hubjab21/high-speed-analog-front-end-pcb/LTspice/lmh5401_test.asc

C1: cap; 5p
C2: cap; 2.2n
C3: cap; 2.2n
C4: cap; 2.2n
R8: res; 50
R9: res; 50
R10: res; 210
R11: res; 210
RF+: res; 100k
RF-: res; 100k
RG+: res; 470
RG-: res; 470
Rin: res; 50
RM: res; 0
RT: res; 100k
U1: LMH5401
V1: voltage; -2.5
V2: voltage; 2.5
Vin: voltage; ""; AC 10m
Named nets: 0, OUT+, OUT-
.include LMH5401.lib
.ac dec 1000 100 1G
.tran 0 1 0 10m
.noise V(OUT+) Vin dec 100 100 100Meg
.measure noise NOISERMS integ V(onoise) from 100 to 100k
